Fenish/decky/DeckSrc/notes/memory/decky-desktop.md

# Decky desktop — 2026-09-10

The user named the project Decky. The Electron desktop was rewritten around shared validated configuration, a main-process action runner, atomic settings, a serial device module, and feature-based React UI. See `desktop/README.md`.

Empty defaults must be pitch black, with no numbers, plus signs or tint. The initial profile is empty. A starter layout is only added explicitly. Assigned action keys support Normal or Toggle behavior with separate OFF/ON images and adjustments. Toggle state is session-local, changes only after a successful action, and is not a claim about OBS or another application's actual state. Soundpad remains future work.

The real OBJ is loaded by Three.js; the user's SVG is white. The generated Obsidian asset and exact prompt live in the renderer assets directory.

Decky v2 firmware was flashed to COM5 (serial a4cb8fcdd274), with hash verification. It starts black and accepts transactional static RGB565 page transfers, eight cached pages, incremental changes, BLANK commands and framebuffer screenshots. Original timing and touch libraries remain. The touch-test application backup is `desktop/output/touch-test-backup.bin` (512 KB, enough to contain that application); factory backup is unchanged. GIF/SD libraries remain historical, dormant code.

Verified: 18 unit tests; headless browser interaction checks for empty defaults, separate OFF/ON uploads, adjustments, toggle success/failure, Back placement and dirty-edit protection; desktop build; firmware build/flash; actual framebuffer confirmed 384,000 black pixels at startup. Hardware measured cached navigation at 81 ms and first single-key update at 2198 ms. Test artifacts and a framebuffer preview are under ignored `desktop/output/`. A Windows unpacked executable was built. Interactive Electron UX and the user's touch-feel check have not been completed.

## Development startup fix

Electron 44.3.0 has no postinstall lifecycle hook and downloads its executable on demand through its package entry point. electron-vite 5 reads Electron's `path.txt` directly instead, resulting in **Error: Electron uninstall** even though the npm package exists. This was reproduced from the installed source. `scripts/ensure-electron.mjs` now checks the executable/version and invokes Electron's official installer when needed. Both `dev` and `preview` run this before electron-vite. The runtime was installed and its `--version` command returned `v44.3.0`.

The user asked to leave feature work as-is for now and fix development startup. Continue from that scope; do not restart feature expansion automatically.

## Current UI, superseding the earlier pause

The user approved and requested the floating-grid dashboard with a contextual right editor. It is now implemented. Empty keys open an action picker; assigned keys open the matching compact form. Closing the panel recenters the deck. Dock: Keys, selected-key Appearance, Pages, Settings. No permanent sidebar, slogans, device specs or activity feed.

Disconnected artwork was regenerated as smooth black obsidian with ivory edge lights; no grain, noisy/mottled material or desk props. The real OBJ is centered with studio lighting. The model/title were reduced in size. There is no retry button: discovery repeats every four seconds. Connection rotates face-on, zooms through the center aperture, then reveals the dashboard; it cancels on detected disconnection and respects reduced motion.

The custom title bar shows the tightly cropped white user logo beside Decky. Minimize, maximize/restore and close use validated IPC; close keeps the app in the tray. The app/tray icon is white with transparency, not a dark tile, at 16–256 ICO sizes and a 512px PNG. `scripts/build-icons.mjs` reproduces it without changing the original branding.

Labels can be empty; label-free icons center vertically. Appearance offers a per-state key background color. Both frontend rendering and device RGB565 encoding use it, while unassigned cells stay black. Configuration remains backward compatible.

Earlier checks: 20 unit tests, lint/typecheck/build, headless dashboard flows and connection transition tests. Windows unpacked executable was rebuilt at that stage. Native window gestures still benefit from the user's interactive check.

## Latest requested refinements and firmware v3

Program typeahead scans Start Menu, App Paths and Store manifests, with real native application icons (OpenVPN Connect discovery/icon verified on this computer). Lucide search spans the complete installed icon set; empty search shows 24 useful defaults. Images support 10–400% zoom and hover-X removal. Labels use the accent color. Icon/text spacing centers the group and moves both toward each other. Appearance, header and selected grid draft use the same canvas renderer; OFF/ON preview selection stays consistent before Save.

Dock now duplicates the selected key. Drag/drop moves to an empty cell or swaps occupied cells; Back stays protected and dirty edits are guarded. Toggle runtime state follows moves. Scripts default to background, waiting, 30 seconds. Disable waiting for an independent session with no timeout; disable background for a visible PowerShell window. Independent executions don't block other keys. Managed cancellation covers the runner's active jobs.

Firmware v3 was flashed on COM5, MAC a4cb8fcdd274, at 460800 with Hash of data verified. V2 rollback binary is desktop/output/decky-v2-backup.bin. The eight advertised page slots have two extra staging slots, preserving the old visible page and all cached pages during updates. The host prepares all configured pages on connection/reset and refreshes changed pages. The current user profile has three pages. More than eight produces an explicit capacity notice and active-page fallback. Firmware initially shows the white user logo plus progress in the center key. BYE shows Disconnected immediately; missing main-process heartbeats for 12 seconds also does. Tray-hidden apps keep heartbeats running. Device reset signals trigger warmup again.

Hardware check tools/check_cache.py populated eight pages, replaced all eight while an old page stayed active, then verified every page was still cached. Measured cached switches 78.3–84.1 ms. Watchdog and BYE both passed. Framebuffer PNGs of the actual loading and disconnected screens were inspected in desktop/output/. Test ends offline without changing the user's saved profile. Firmware built once for this revision. Desktop was built for QA, with one incremental rebuild after fixing refresh of an inactive page; avoid repeated full builds per user request. The packaged executable predates these latest refinements; use the normal development command to run current source.

## Firmware v4: alternating toggle freeze fixed

The user reported stalls when alternating Mute and Deafen. Whole-page state snapshots caused new RGB565 transfers for different toggle combinations. V4 preloads each toggle's OFF and ON image independently: OFF images are the base page, ALT transfers ON images once, STATE selects a per-key bitmask. Main-process successful actions send STATE directly; deviceReady stays true, and renderer runtime state changes no longer trigger page rendering/uploads. Firmware draws only changed cells (zero for an unchanged mask). Edited ON artwork marks its cell dirty so a same-state refresh still repaints. CRC failures preserve the prior alternate; allocations retain the PSRAM floor. Old snapshot allocations/alternates are freed when superseded.

V4 flashed to re-enumerated COM5, verified MAC a4cb8fcdd274 and Hash of data verified. V3 rollback: desktop/output/decky-v3-backup.bin. Hardware tools/check_toggles.py alternated two toggles 100 times: zero image uploads, 5.48–20.47 ms per state change (mean 11.72 ms), one-cell redraws. Actual framebuffer confirmed both ON images and the third unchanged key. Test finishes disconnected and preserves saved profile. Main-process integration test covers all four combinations repeatedly without PUSH/CACHE calls after preload; UI test confirms no renderer sync on state changes. Full suite: 41 passed, one optional installed-app discovery test skipped; typecheck/build/lint and UI passed. Only one desktop build and one firmware build were run for this fix. User launches current desktop source; installed/unpacked package may be older.

## Firmware v5: Wireless Settings

User requested Wi-Fi list, selection and wireless use. Settings now scans on the deck, shows signal/security, accepts the network password, polls connection progress, and switches USB↔Wi-Fi. ESP32-S3 supports 2.4 GHz; PC may be wired or wireless on the same LAN. Power still comes from USB. The user chooses the real network in the application; no network was selected on their behalf.

New firmware wireless.cpp/h provides asynchronous scans, connection/reconnection, NVS credentials, authenticated TCP 47561, UDP discovery 47562, and separate command-reply/event transport ownership. The serial command protocol and 128-byte image ACKs are reused over TCP; per-key toggle caching stays intact. Initial USB setup retrieves a random 256-bit pairing key; the desktop saves it using safeStorage/Windows protection in wifi-pair.json, separate from the profile. Network authentication uses fresh HMAC-SHA256 challenges and a server proof. No Wi-Fi password or pairing secret is returned to the renderer or recorded in diagnostics. Configuration commands require USB. Alternate IP discovery and USB fallback are implemented.

V5 built with unchanged pinned toolchain/partition layout (1,079,648-byte app), flashed to verified COM5/MAC a4cb8fcdd274 after the user quit the tray app, with Hash of data verified. Rollback is desktop/output/decky-v4-backup.bin. Real USB scan found one network in 2534 ms and pairing availability passed, without joining. Local socket tests validate mutual pairing, reject an invalid server proof/early key event, and transfer full binary artwork correctly. UI scan/password/connect/transport flow passed with fixture credentials; screenshot output/decky-wifi-settings.png inspected. Real-router authentication and wireless operation await the user choosing their network in Settings. Current app source/out are updated; an older packaged executable is not rebuilt.

User then reported the physical screen shifting upward after Wi-Fi was added. Captured framebuffer remained correctly centered (output/wifi-shift-framebuffer.png): evidence points to RGB DMA/scanout desynchronization, not a grid-coordinate error. ESP-IDF's RGB docs explicitly describe permanent drift when PSRAM bounce-buffer service is interrupted by NVS/flash/Wi-Fi work. Added Bus_RGB::restartScanout using esp_lcd_rgb_panel_restart (scheduled by IDF at vertical blank), panel::recover_scanout, and task-context recovery windows around Wi-Fi startup/events/scans/connection and credential writes. Kept the actual existing pixel clock, 48-line bounce buffer, porch values and key geometry unchanged (some older notes incorrectly say 40 or 64 lines). DISPLAY_RESYNC provides a bounded diagnostic recovery command. A physical visual check is needed because a framebuffer capture cannot show scanout drift.

Display recovery patch flashed with Hash of data verified. Repeated Wi-Fi scan passed (8 networks, 3049 ms) and DISPLAY_RESYNC succeeded. User confirmed the physical alignment was fixed. Wireless Settings is ready for their network selection; no real Wi-Fi credentials were supplied to the agent.

## Firmware v6: persistent artwork and fast wireless boot

User reported five-minute wireless startup and requested all states stored on-device/SD. V6 negotiates 4096-byte TCP blocks instead of serial's 128-byte ACK blocks, uses bulk socket reads, and sends each ACK in one write. Serial remains at its tested 128-byte block size. No changes to GPIO/display timing/recovery.

Added artwork_store.cpp: mounts existing TF card on SPI2/FSPI (CLK12, MISO13, MOSI11, CS10), never formats. Stores sparse base pages and independent ON images in /decky-cache, bounded by page/cell IDs. Header includes schema, sizes, CRC, lit mask. Temporary/backup rename handles interrupted writes; length/CRC rejects corrupt/stale data, causing a normal reupload. Cached files load into PSRAM when requested at startup; no full-page toggle combinations needed. SD failures are reported while memory-based operation remains possible. Settings reports card availability.

Found the installed 15,931,539,456-byte card. V6 flashed to verified COM5/MAC a4cb8fcdd274 with Hash of data verified; V5 rollback at desktop/output/decky-v5-backup.bin. Prepared user's actual three-page profile and two ON images with the existing canvas renderer, without modifying configuration or executing actions. tools/check_persistent.py authenticated over the real Wi-Fi connection, saved all artwork, hard-reset the board, and checked restoration: first save 8805 ms / 21 images / 609588 bytes; after reboot 1569 ms / zero image uploads / five cache hits; reset to ready including Wi-Fi reconnection 9714 ms. Evidence desktop/output/persistent-cache-check.json. Test finishes with BYE; user should reopen current desktop. Artwork is already on the SD card.

Validation: 51 tests passed, one optional discovery test skipped; typecheck/build, UI workflow and real wireless cold/warm reboot passed. Prepared profile artifacts live under desktop/output/prepared-profile and contain artwork only, no Wi-Fi secret. Pairing secret used for hardware check stayed in memory. Existing unrelated changes from concurrent work (hotkey/transport tests and UI refinements) were retained.
