Fenish/decky/DeckSrc/notes/memory/no-visible-screws.md

---
name: no-visible-screws
type: preference
---

No screws may be visible on the top cover. All fastening happens from
underneath.

**Why it matters:** rules out the obvious top-down assembly order; any new
fastener has to be reachable from the bottom of the case.
