Fenish/decky/DeckSrc/firmware/src/deck/decky_logo.h

#pragma once
#include <Arduino.h>
constexpr int DECKY_LOGO_SIZE = 72;
static const uint8_t DECKY_LOGO_ALPHA[] PROGMEM = {
0,0,0,0,0,0,0,0,0,0,0,0,0,0,0,0,0,0,0,0,0,0,0,0,
0,0,0,0,0,0,0,4,0,0,87,52,0,0,3,0,0,0,0,0,0,0,0,0,
0,0,0,0,0,0,0,0,0,0,0,0,0,0,0,0,0,0,0,0,0,0,0,0,
0,0,0,0,0,0,0,0,0,0,0,0,0,0,0,0,0,0,0,0,0,0,0,0,
0,0,0,0,0,1,2,0,50,189,255,245,141,16,0,3,1,0,0,0,0,0,0,0,
0,0,0,0,0,0,0,0,0,0,0,0,0,0,0,0,0,0,0,0,0,0,0,0,
0,0,0,0,0,0,0,0,0,0,0,0,0,0,0,0,0,0,0,0,0,0,0,0,
0,0,0,0,2,0,0,117,249,255,253,255,255,222,78,0,0,2,0,0,0,0,0,0,
0,0,0,0,0,0,0,0,0,0,0,0,0,0,0,0,0,0,0,0,0,0,0,0,
0,0,0,0,0,0,0,0,0,0,0,0,0,0,0,0,0,0,0,0,0,0,0,0,
0,0,0,3,0,13,169,255,255,252,255,254,251,255,255,148,8,0,3,0,0,0,0,0,
0,0,0,0,0,0,0,0,0,0,0,0,0,0,0,0,0,0,0,0,0,0,0,0,
0,0,0,0,0,0,0,0,0,0,0,0,0,0,0,0,0,0,0,0,0,0,0,0,
0,0,3,0,27,204,255,251,254,255,255,255,255,253,252,255,199,29,0,4,0,0,0,0,
0,0,0,0,0,0,0,0,0,0,0,0,0,0,0,0,0,0,0,0,0,0,0,0,
0,0,0,0,0,0,0,0,0,0,0,0,0,0,0,0,0,0,0,0,0,0,0,0,
0,3,0,35,219,255,251,255,255,255,255,255,255,255,255,250,255,224,45,0,4,0,0,0,
0,0,0,0,0,0,0,0,0,0,0,0,0,0,0,0,0,0,0,0,0,0,0,0,
0,0,0,0,0,0,0,0,0,0,0,0,0,0,0,0,0,0,0,0,0,0,0,0,
2,0,35,225,255,251,255,255,255,255,252,253,255,255,255,255,251,255,236,59,0,4,0,0,
0,0,0,0,0,0,0,3,1,0,0,0,0,0,0,0,0,0,0,0,0,0,0,0,
0,0,0,0,0,0,0,0,0,0,0,0,0,0,0,0,0,0,0,0,0,0,0,2,
1,21,220,255,251,255,255,255,255,253,255,255,252,255,255,255,255,252,255,245,64,0,4,0,
0,0,0,0,0,2,1,0,0,1,0,0,0,0,0,0,0,0,0,0,0,0,0,0,
0,0,0,0,0,0,0,0,0,0,0,0,0,0,0,0,0,0,0,0,0,0,1,3,
2,190,255,251,255,255,255,255,252,255,190,208,255,252,255,255,255,255,252,255,243,59,0,2,
0,0,0,1,4,0,0,75,11,0,3,0,0,0,0,0,0,0,0,0,0,0,0,0,
0,0,0,0,0,0,0,0,0,0,0,0,0,0,0,0,1,3,4,2,0,0,3,0,
122,255,250,255,255,255,255,251,255,157,0,9,161,255,252,254,255,255,255,252,253,250,43,1,
2,0,3,0,0,37,175,255,196,25,0,3,0,0,0,0,0,0,0,0,0,0,0,0,
0,0,0,0,0,0,0,0,0,0,0,0,0,0,3,3,0,0,0,0,0,2,1,37,
247,252,254,255,255,255,251,255,145,0,3,0,0,119,255,254,254,255,251,255,255,190,35,1,
3,3,0,5,118,241,255,250,255,218,36,0,3,0,0,0,0,0,0,0,0,0,0,0,
0,0,0,0,0,0,0,0,0,0,0,0,3,1,0,0,14,64,127,89,0,6,0,157,
255,251,255,255,255,253,255,145,0,3,1,1,4,0,95,253,252,252,255,237,110,0,0,4,
0,0,67,204,255,255,252,255,251,255,225,32,0,2,0,0,0,0,0,0,0,0,0,0,
0,0,0,0,0,0,0,0,0,0,1,3,0,0,62,157,228,255,255,107,0,1,21,241,
254,254,255,255,253,253,145,0,4,1,0,0,0,5,0,85,255,255,163,32,0,4,2,0,
25,155,255,255,251,254,255,255,255,251,255,214,18,1,2,0,0,0,0,0,0,0,0,0,
0,0,0,0,0,0,0,0,0,2,0,0,62,187,255,255,255,253,246,33,0,0,92,255,
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
};
